sparkfun/ESP32_LoRa_1Ch_Gateway/Hardware/Board_Design_Checklist/doc_images/03-default_location.png

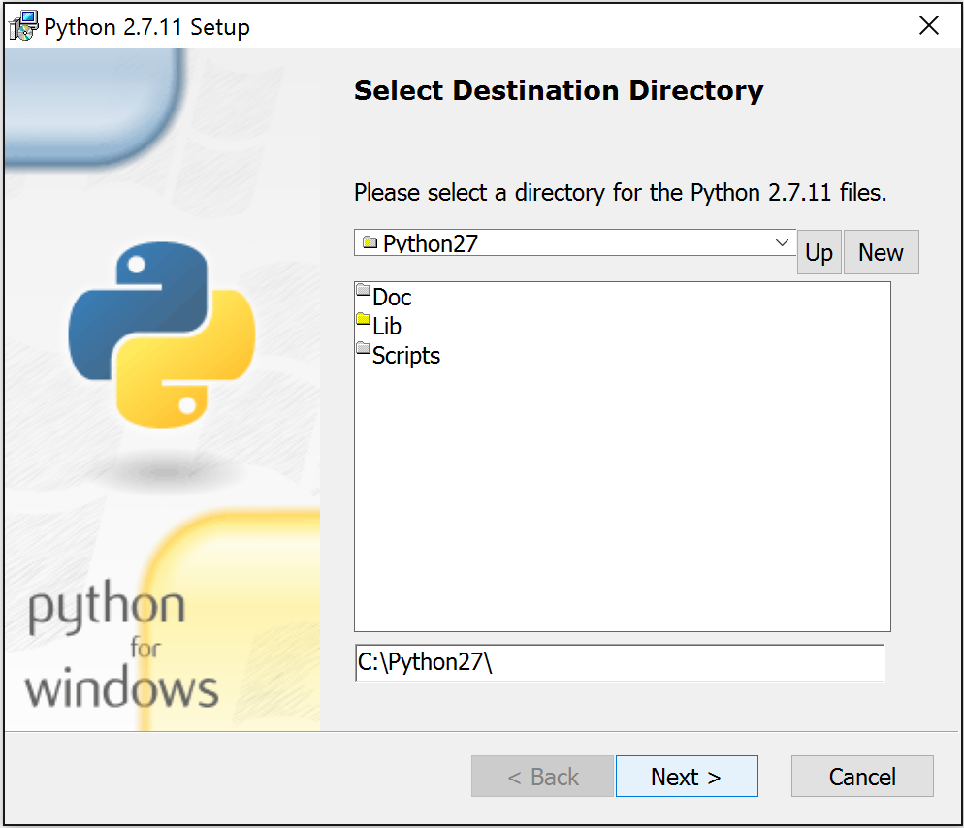
Hardware/Board_Design_Checklist/doc_images/03-default_location.png
