sparkfun/ESP32_LoRa_1Ch_Gateway/Hardware/Board_Design_Checklist/doc_images/04-path.png

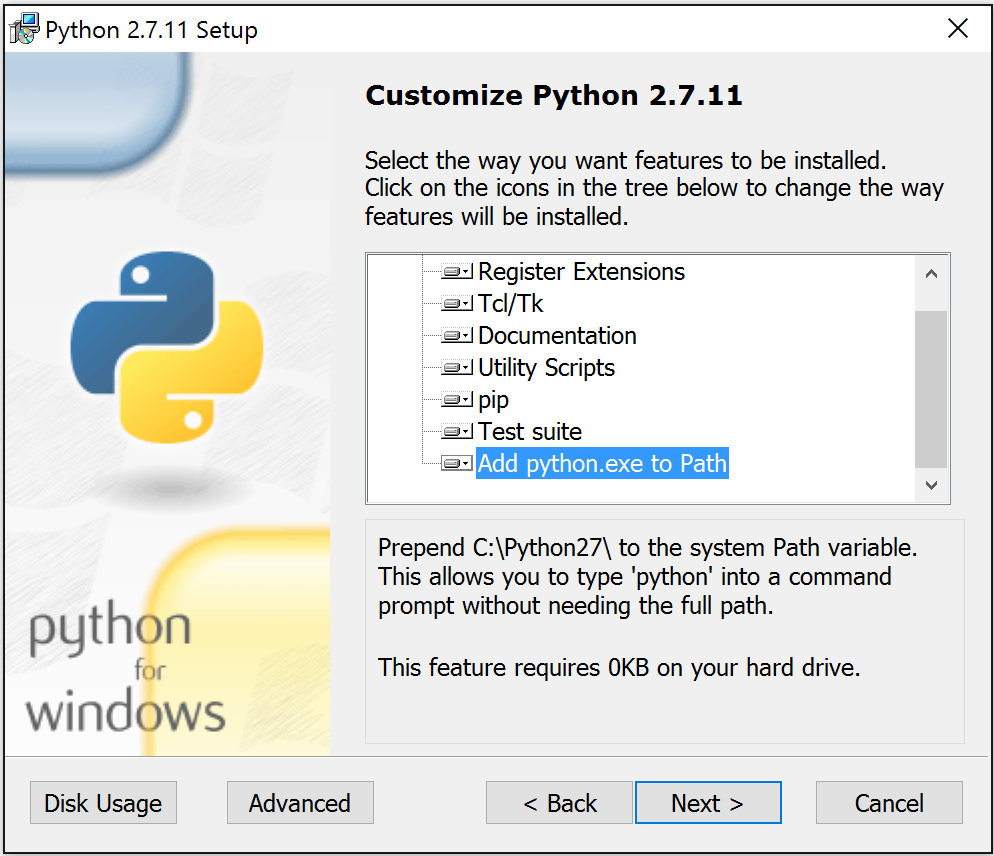
Hardware/Board_Design_Checklist/doc_images/04-path.png
