sparkfun/ESP32_LoRa_1Ch_Gateway/Hardware/Board_Design_Checklist/doc_images/06-env_settings.png

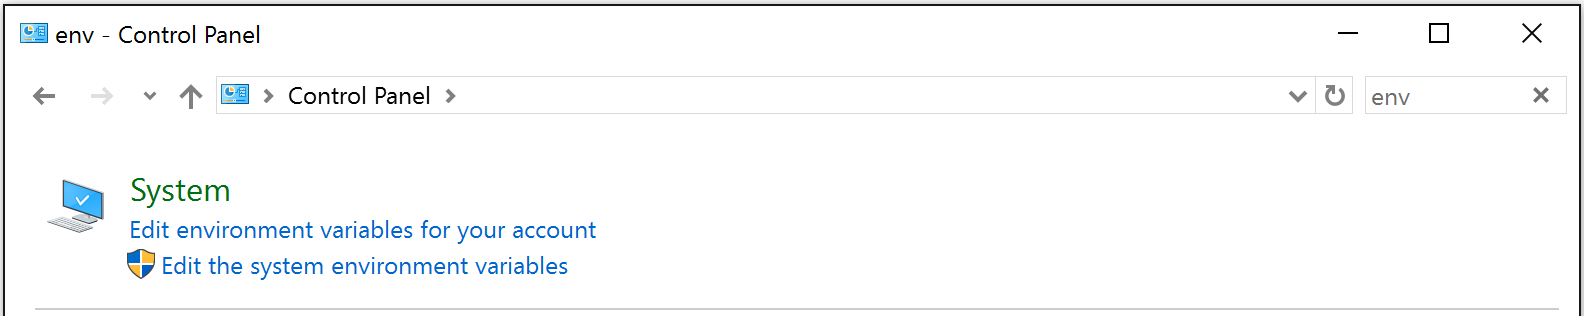
Hardware/Board_Design_Checklist/doc_images/06-env_settings.png
