sparkfun/ESP32_LoRa_1Ch_Gateway/Hardware/Board_Design_Checklist/Excel_Modules_Installation/xlrd-0.9.3/tests/xf_class.xls

Sheet: table1
RED | RED
GREEN | GREEN
BLUE | BLUE
LEFT | CENTER | RIGHT
TOP | MIDDLE | BOTTOM
borderstyle

Sheet: table2
MERGED

Sheet: table3
RED | RED
GREEN | GREEN
BLUE | BLUE
