sparkfun/ESP32_LoRa_1Ch_Gateway/Hardware/Board_Design_Checklist/Excel_Modules_Installation/xlwt-0.7.5/tests/RKbug1.xls

actual | expected | OK | actual | expected | OK
130.64 | 130.63999999999999 |  | 1.3064 | 1.3063999999999998
130.64 | 130.63999999999999 |  | 1.3064 | 1.3063999999999998
-18.65 | -18.649999999999999 |  | -0.1865 | -0.1865
-18.65 | -18.649999999999999 |  | -0.1865 | -0.1865
137.2 | 137.19999999999999 |  | 1.372 | 1.3719999999999999
137.2 | 137.19999999999999 |  | 1.372 | 1.3719999999999999
-16.08 | -16.079999999999998 |  | -0.1608 | -0.16079999999999997
-16.08 | -16.079999999999998 |  | -0.1608 | -0.16079999999999997
0 | 0.0 |  | 0 | 0.0
1 | 1.0 |  | 0.01 | 0.01
2 | 2.0 |  | 0.02 | 0.02
3 | 3.0 |  | 0.03 | 0.029999999999999999
536870911 | 536870911.0 |  | 5368709.11 | 5368709.1100000003
536870912 | 536870912.0 |  | 5368709.12 | 5368709.1200000001
536870913 | 536870913.0 |  | 5368709.13 | 5368709.1299999999
1000999999 | 1000999999.0 |  | 10009999.99 | 10009999.99
1073741823 | 1073741823.0 |  | 10737418.23 | 10737418.23
1073741824 | 1073741824.0 |  | 10737418.24 | 10737418.24
1073741825 | 1073741825.0 |  | 10737418.25 | 10737418.25
2147483647 | 2147483647.0 |  | 21474836.47 | 21474836.469999999
2147483648 | 2147483648.0 |  | 21474836.48 | 21474836.48
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
