sparkfun/ESP32_LoRa_1Ch_Gateway/Hardware/Board_Design_Checklist/Excel_Modules_Installation/xlutils-1.7.1/xlutils/tests/test.xls

Sheet: Sheet1
R0C0 | R0C1
R1C0 | R1C1

Sheet: Sheet2
R0C0 | R0C1
R1C0 | R1C1
